Shame5800/CRT-Telecaster/Src 7-3-2026/global.cpp

#include "global.h"

portMUX_TYPE mux = portMUX_INITIALIZER_UNLOCKED;
volatile uint32_t phaseIncrementChannelOne = 0;
volatile uint32_t phaseIncrementChannelTwo = 0;
volatile uint32_t phaseIncrementChannelThree = 0;
volatile uint32_t phaseIncrementChannelFour = 0;
volatile int multiplierChannelOne = 0;
volatile int multiplierChannelTwo = 0;
volatile int multiplierChannelThree = 0;
volatile int multiplierChannelFour = 0;
volatile int pulsePot=0;
SPIClass spi(VSPI);

volatile int waveSelector=0;

TaskHandle_t dacTaskHandle = NULL;

const uint8_t sineTable[256] = {
  50,51,53,54,55,56,57,58,60,61,62,63,64,65,67,68,
  69,70,71,73,74,75,76,77,78,79,80,81,82,83,84,85,
  86,87,88,89,90,91,91,92,93,94,95,95,96,96,97,97,
  98,98,98,99,99,100,100,100,100,100,100,100,100,100,100,100,
  100,100,100,100,100,100,100,100,99,99,98,98,98,97,97,96,
  96,95,95,94,93,92,91,91,90,89,88,87,86,85,84,83,
  82,81,80,79,78,77,76,75,74,73,71,70,69,68,67,65,
  64,63,62,61,60,58,57,56,55,54,53,51,50,49,47,46,
  45,44,43,42,40,39,38,37,36,35,33,32,31,30,29,27,
  26,25,24,23,22,21,20,19,18,17,16,15,14,13,12,11,
  10,9,9,8,7,6,5,5,4,4,3,3,2,2,2,1,
  1,1,0,0,0,0,0,0,0,0,0,0,0,0,0,0,
  0,0,0,0,0,0,0,0,0,0,1,1,1,2,2,2,
  3,3,4,4,5,5,6,7,8,9,9,10,11,12,13,14,
  15,16,17,18,19,20,21,22,23,24,25,26,27,29,30,31,
  32,33,35,36,37,38,39,40,42,43,44,45,46,47,49,50
};

const uint8_t triangleTable[256] = {
  100, 99, 98, 98, 97, 96, 95, 95, 94, 93, 92, 91, 91, 90, 89, 88,
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
  51,  50,  49,  48,  47,  46,  45,  43,  42,  41,  40,  39,  38,  36,  35,  34,
  33,  32,  30,  29,  28,  27,  25,  24,  23,  22,  20,  19,  18,  17,  15,  14,
  13,  12,  10,   9,   8,   6,   5,   4,   3,   1,   0,   0,   0,   0,   0,   0,
};
