Shame5800/CRT-Telecaster/Src 7-3-2026/notes.h

#define Bb0  29
#define B0note   30 
#define C1   33
#define Db1  35   // C#1 / Db1
#define D1   37
#define Eb1  39   // D#1 / Eb1
#define E1   41
#define F1   44
#define Gb1  46   // F#1 / Gb1
#define G1   49
#define Ab1  52   // G#1 / Ab1
#define A1   55
#define Bb1  58   // A#1 / Bb1
#define B1note   62
#define C2   65
#define Db2  69   // C#2 / Db2
#define D2   73
#define Eb2  78   // D#2 / Eb2
#define E2   82
#define F2   87
#define Gb2  92   // F#2 / Gb2
#define G2   98
#define Ab2  104  // G#2 / Ab2
#define A2   110
#define Bb2  117  // A#2 / Bb2
#define B2   123
#define C3   131
#define Db3  139  // C#3 / Db3
#define D3   147
#define Eb3  156  // D#3 / Eb3
#define E3   165
#define F3   175
#define Gb3  185  // F#3 / Gb3
#define G3   196
#define Ab3  208  // G#3 / Ab3
#define A3   220
#define Bb3  233  // A#3 / Bb3
#define B3   247
#define C4   262
#define Db4  277  // C#4 / Db4
#define D4   294
#define Eb4  311  // D#4 / Eb4
#define E4   330
#define F4   349
#define Gb4  370  // F#4 / Gb4
#define G4   392
#define Ab4  415  // G#4 / Ab4
#define A4   440
#define Bb4  466  // A#4 / Bb4
#define B4   494
#define C5   523
#define Db5  554  // C#5 / Db5
#define D5   587
#define Eb5  622  // D#5 / Eb5
#define E5   659
#define F5   698
#define Gb5  740  // F#5 / Gb5
#define G5   784
#define Ab5  831  // G#5 / Ab5
#define A5   880
#define Bb5  932  // A#5 / Bb5
#define B5   988
#define C6   1047
#define Db6  1109  // C#6 / Db6
#define D6   1175
#define Eb6  1245  // D#6 / Eb6
#define E6   1319
#define F6   1397
#define Gb6  1480  // F#6 / Gb6
#define G6   1568
#define Ab6  1661  // G#6 / Ab6
#define A6   1760
#define Bb6  1865  // A#6 / Bb6
#define B6   1976
